viswavsn81/jaladarangam/hardware/review/pcb_2d_layout.png

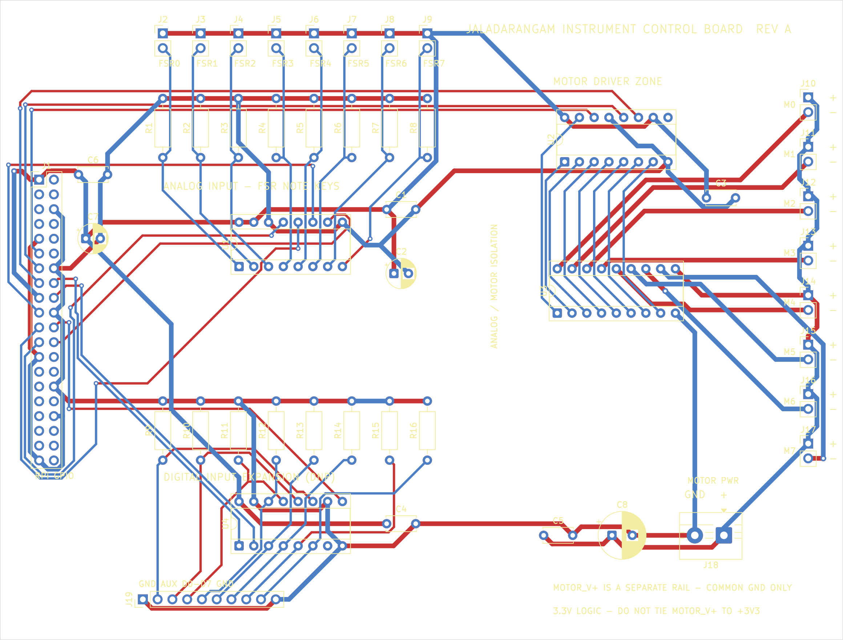
hardware/review/pcb_2d_layout.png
