viswavsn81/jaladarangam/hardware/review/pcb_3d_top.png

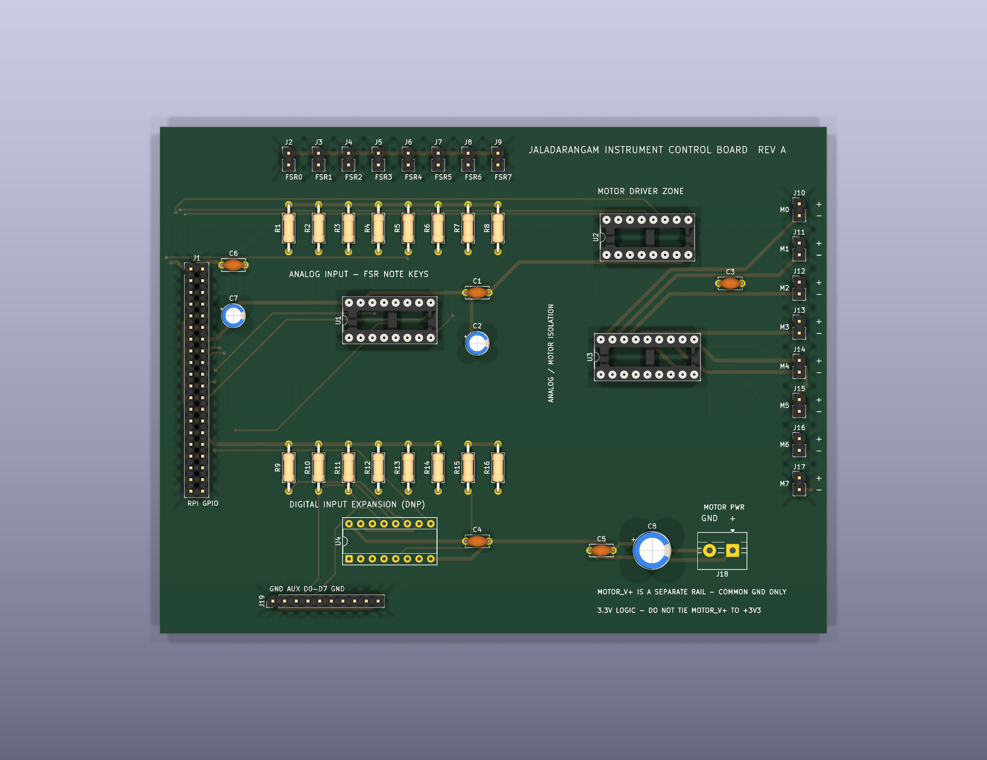
hardware/review/pcb_3d_top.png
