viswavsn81/jaladarangam/hardware/review/silk_aux_header.png

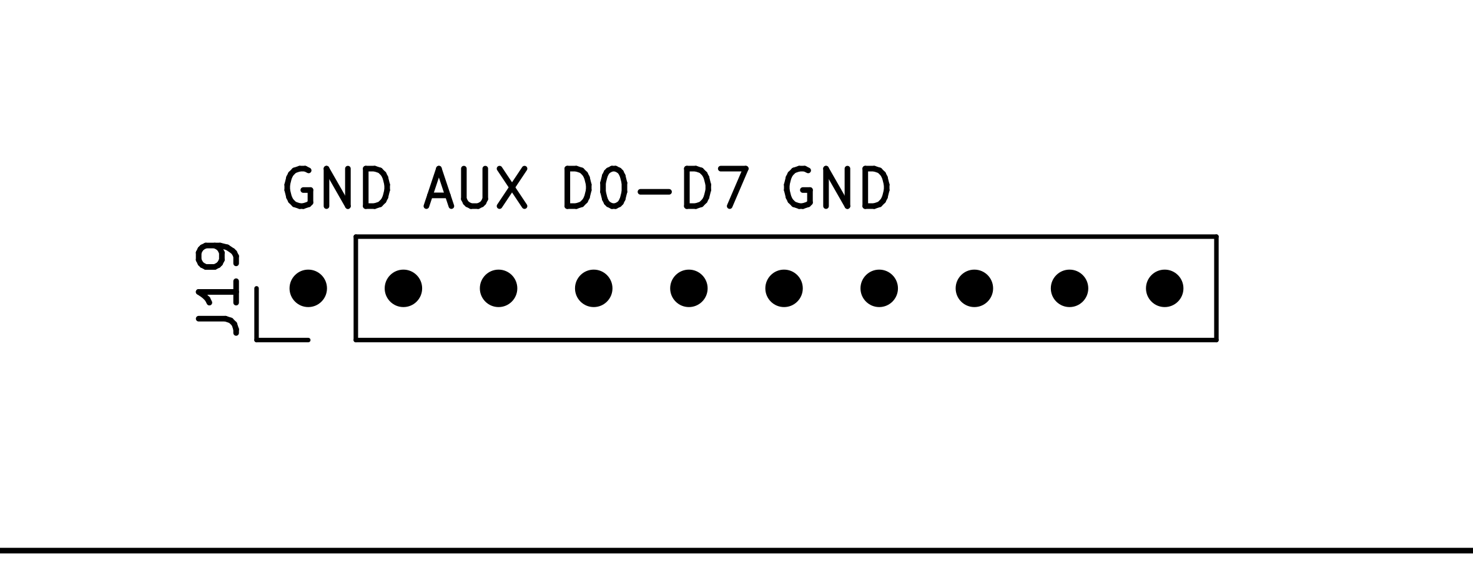
hardware/review/silk_aux_header.png
