viswavsn81/jaladarangam/hardware/review/silk_fsr_headers.png

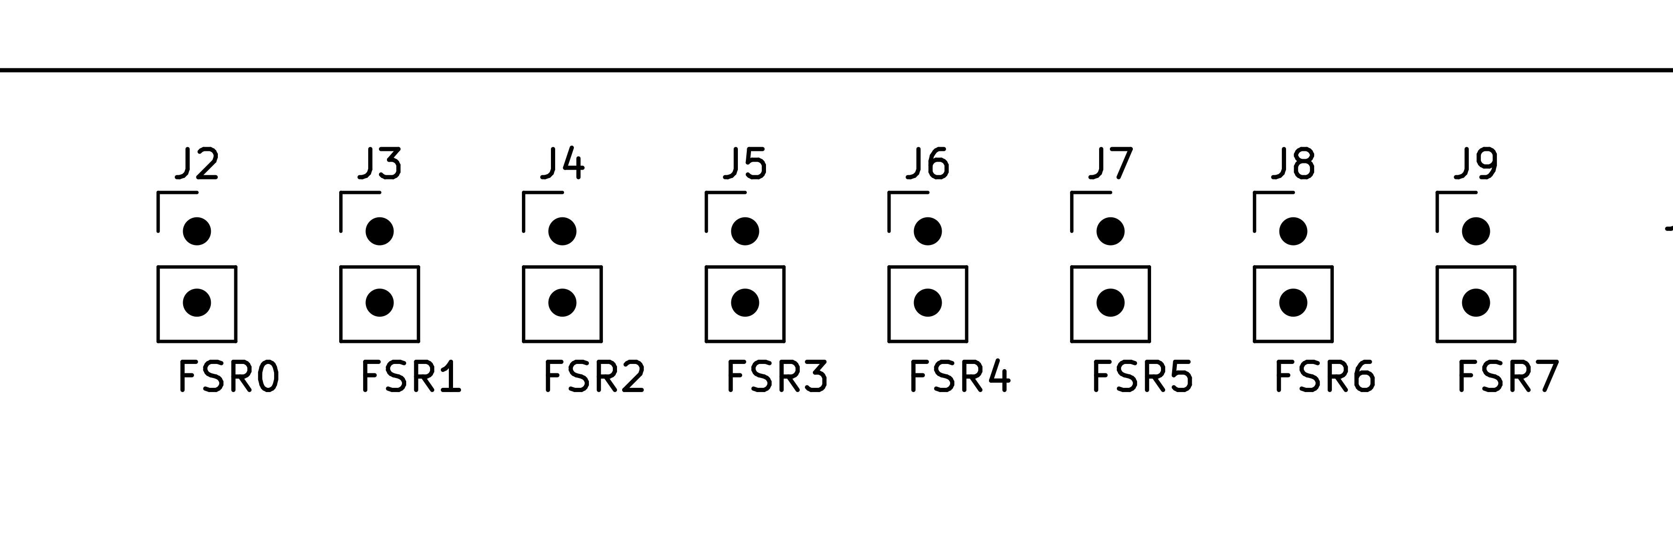
hardware/review/silk_fsr_headers.png
