viswavsn81/jaladarangam/hardware/review/silk_pi_header.png

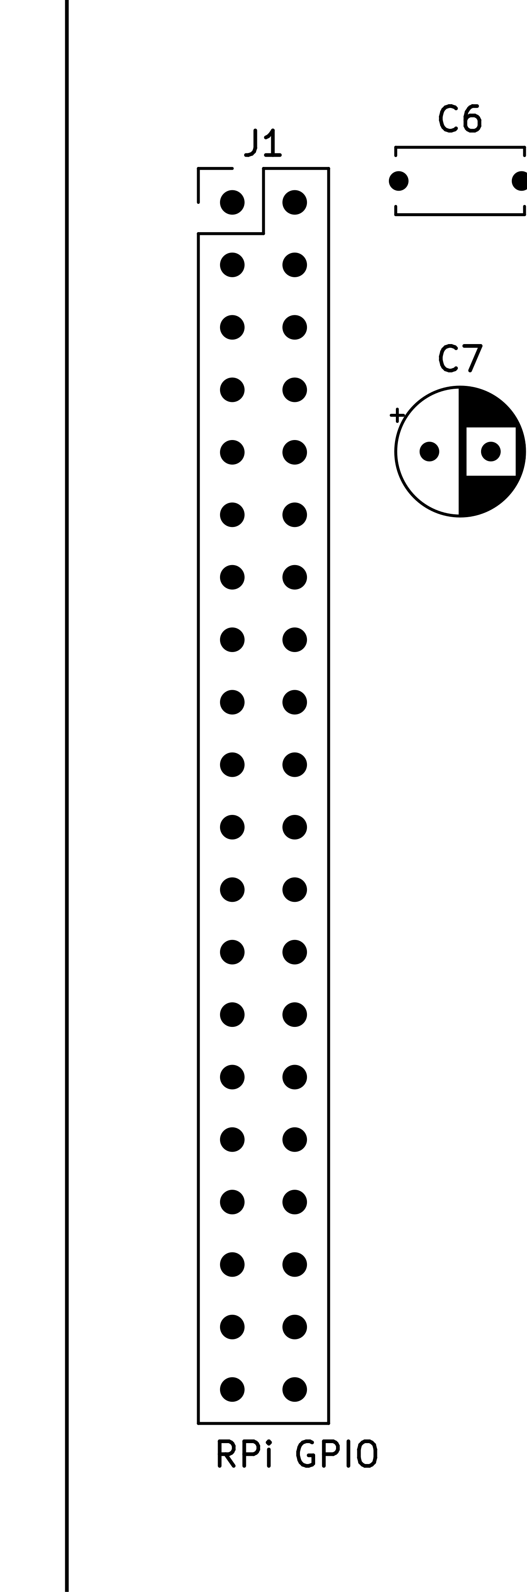
hardware/review/silk_pi_header.png
